stuart-brown/ArduinoShutterSpeedTester/Datasheets/2.2_TFT_LCD/lcdisplay_spi_tft_b-web.jpg

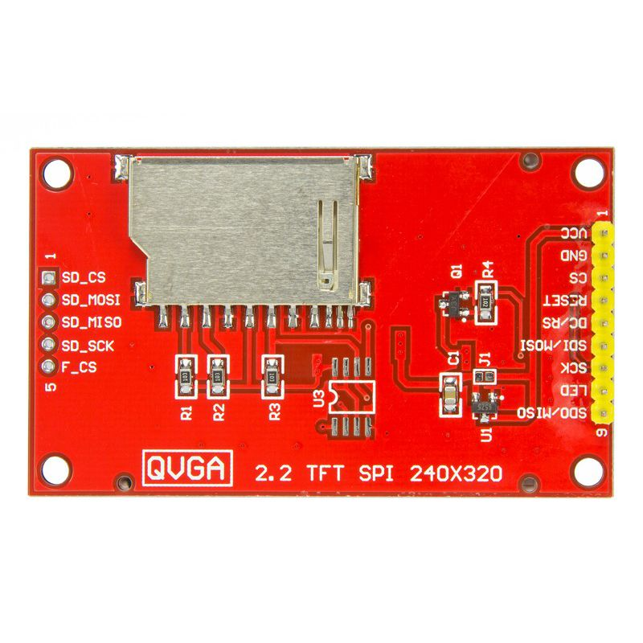
Datasheets/2.2_TFT_LCD/lcdisplay_spi_tft_b-web.jpg
