stuart-brown/ArduinoShutterSpeedTester/Datasheets/2.2_TFT_LCD/p1.jpg

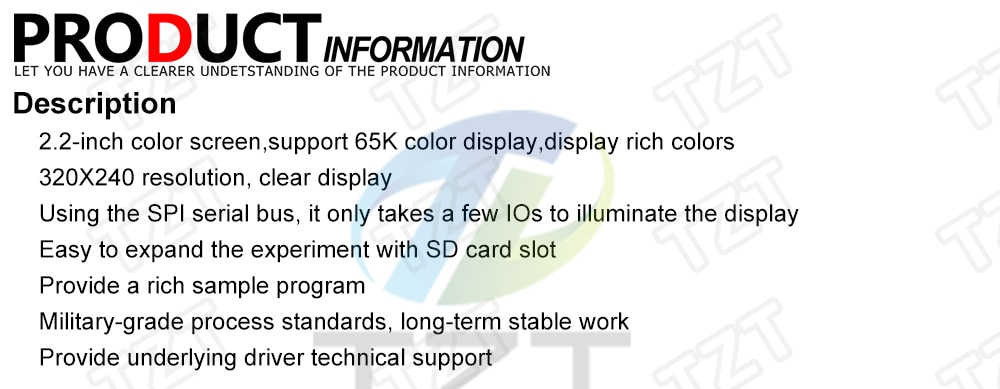
Datasheets/2.2_TFT_LCD/p1.jpg
