stuart-brown/ArduinoShutterSpeedTester/Datasheets/2.2_TFT_LCD/p3.jpg

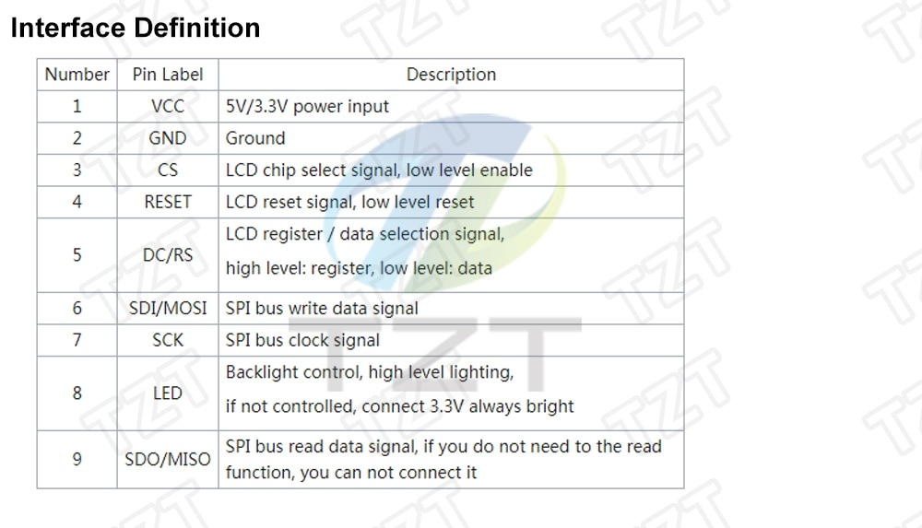
Datasheets/2.2_TFT_LCD/p3.jpg
