stuart-brown/ArduinoShutterSpeedTester/Datasheets/2.2_TFT_LCD/p4.jpg

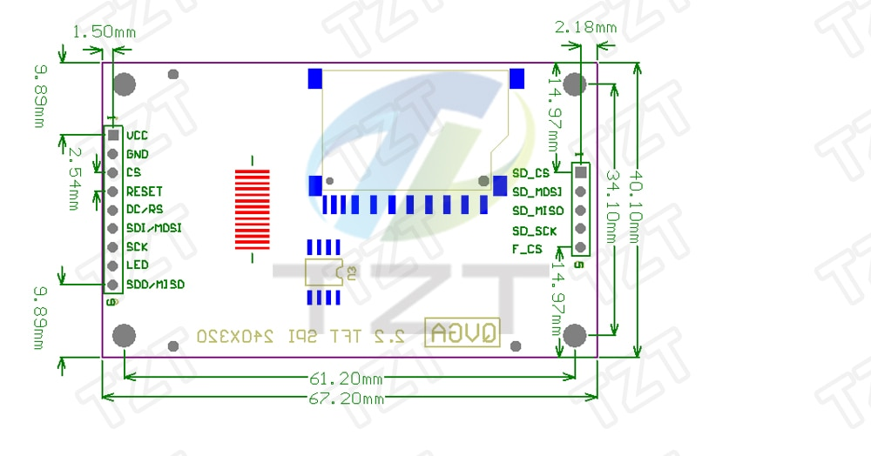
Datasheets/2.2_TFT_LCD/p4.jpg
