stuart-brown/ArduinoShutterSpeedTester/Datasheets/2.2_TFT_LCD/p8.jpg

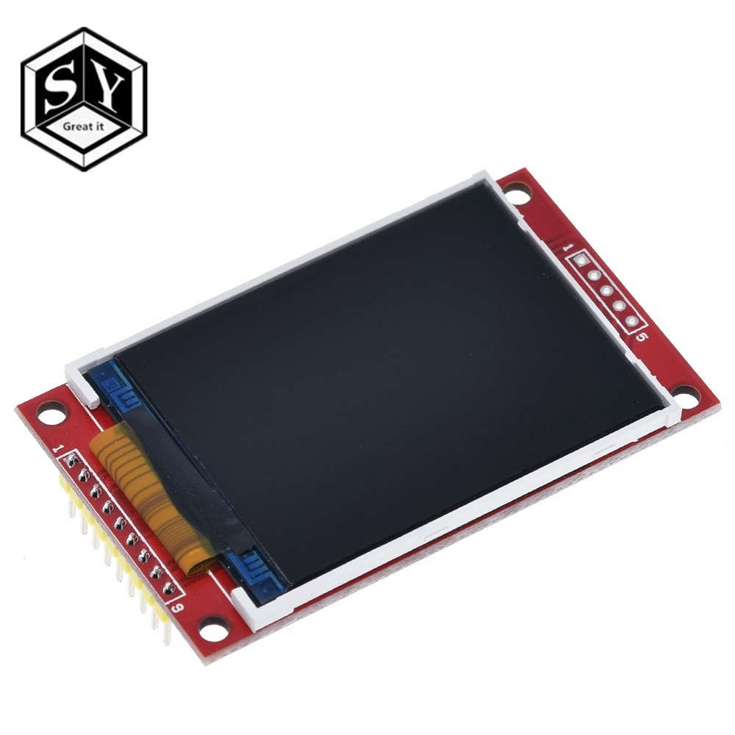
Datasheets/2.2_TFT_LCD/p8.jpg
