stuart-brown/ArduinoShutterSpeedTester/Datasheets/2.2_TFT_LCD/p10.jpg

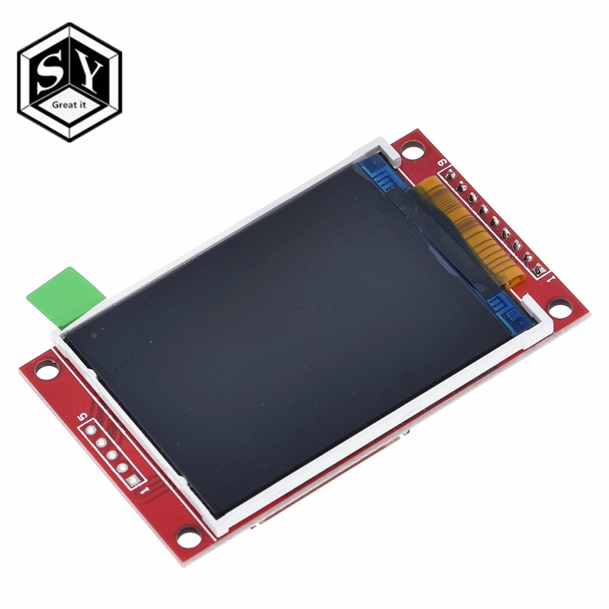
Datasheets/2.2_TFT_LCD/p10.jpg
