stuart-brown/ArduinoShutterSpeedTester/Datasheets/2.2_TFT_LCD/p11.jpg

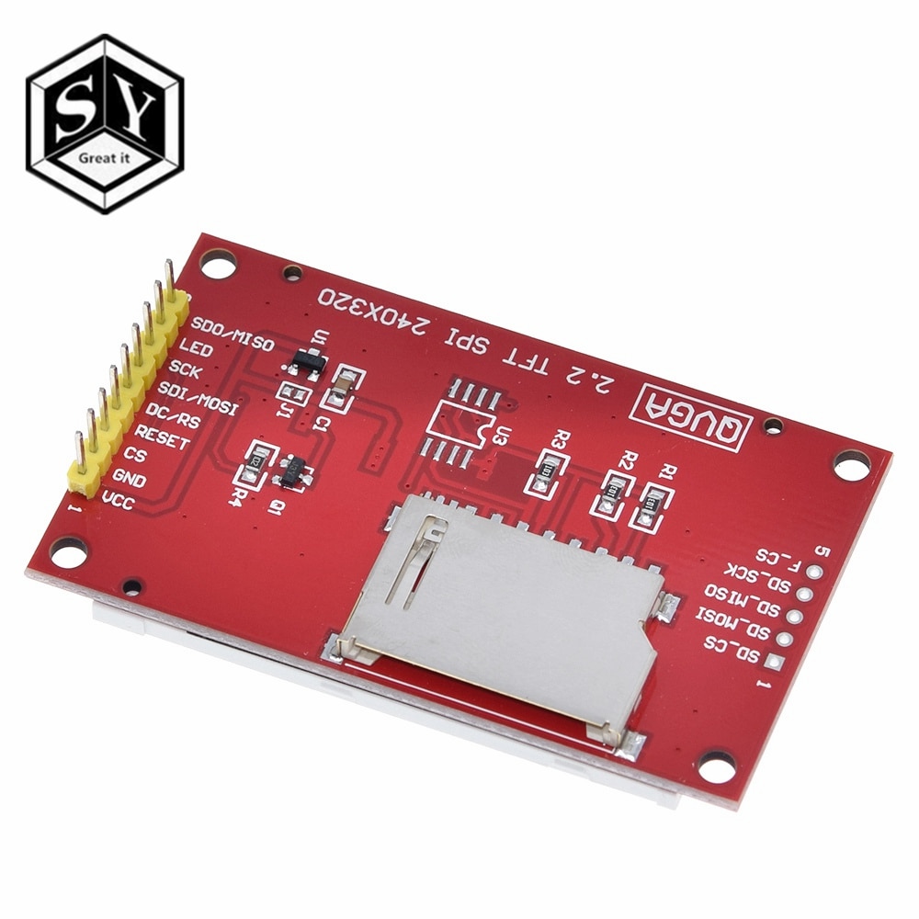
Datasheets/2.2_TFT_LCD/p11.jpg
