stuart-brown/ArduinoShutterSpeedTester/images/Version2/20230103_121651.jpg

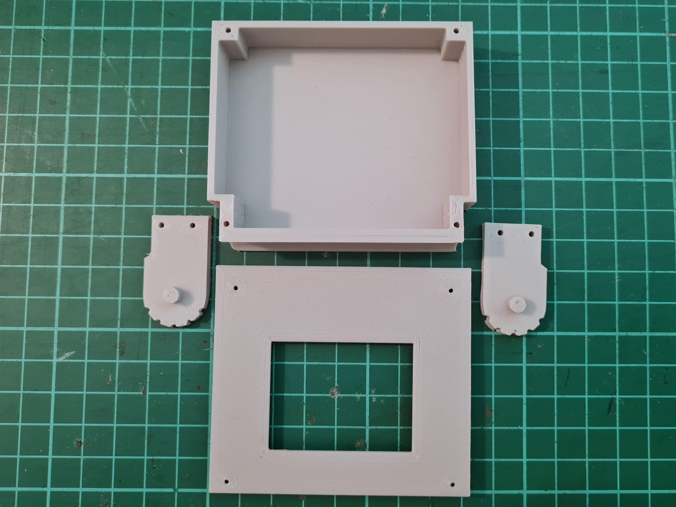
images/Version2/20230103_121651.jpg
