stuart-brown/ArduinoShutterSpeedTester/images/Version2/20230103_121801.jpg

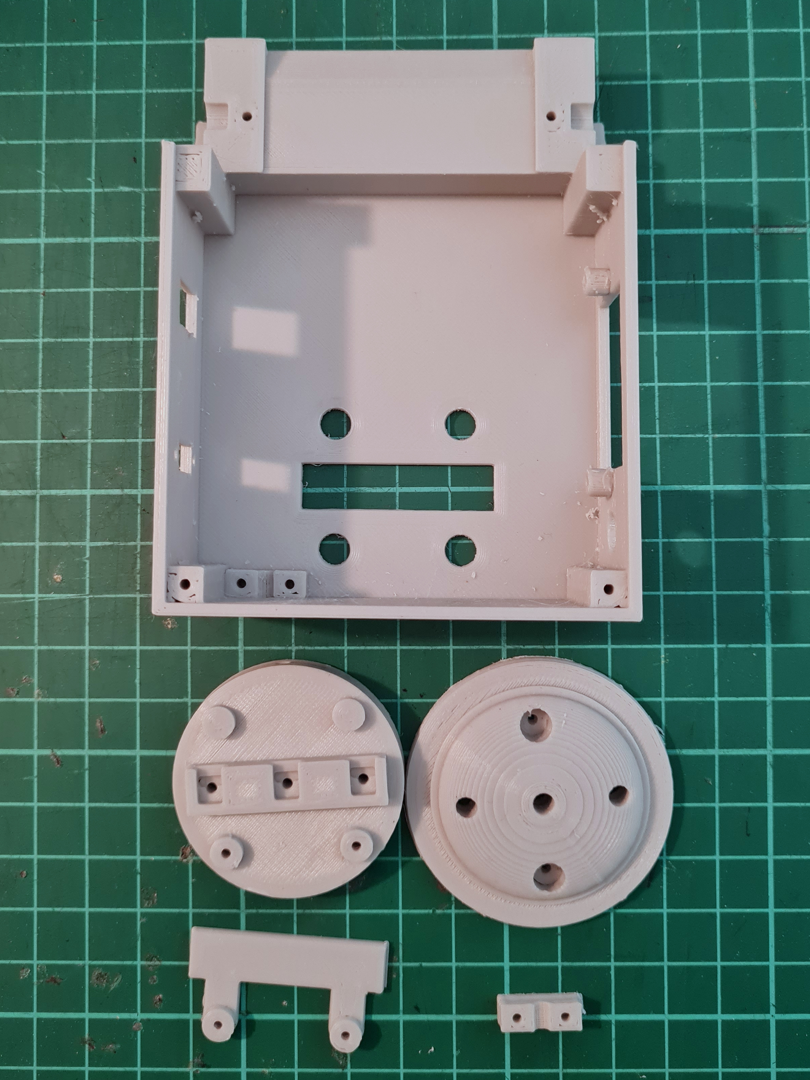
images/Version2/20230103_121801.jpg
