stuart-brown/ArduinoShutterSpeedTester/images/Version2/20230106_110242.jpg

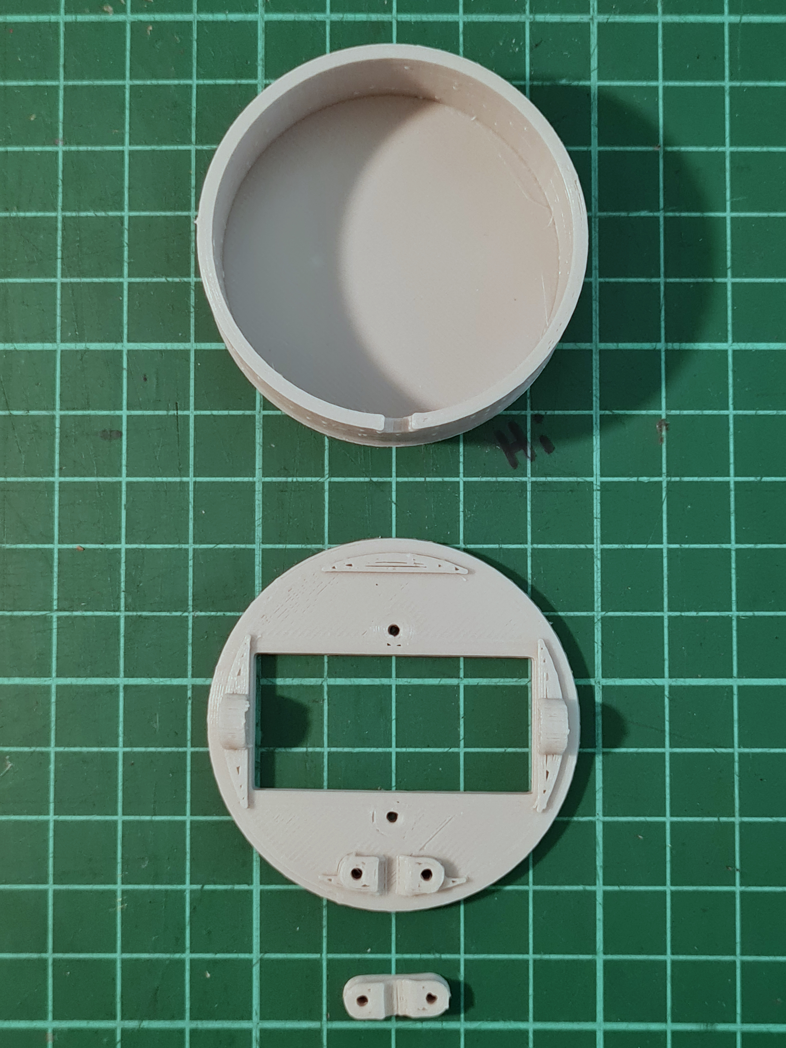
images/Version2/20230106_110242.jpg
