stuart-brown/ArduinoShutterSpeedTester/images/Version2/20230106_110354.jpg

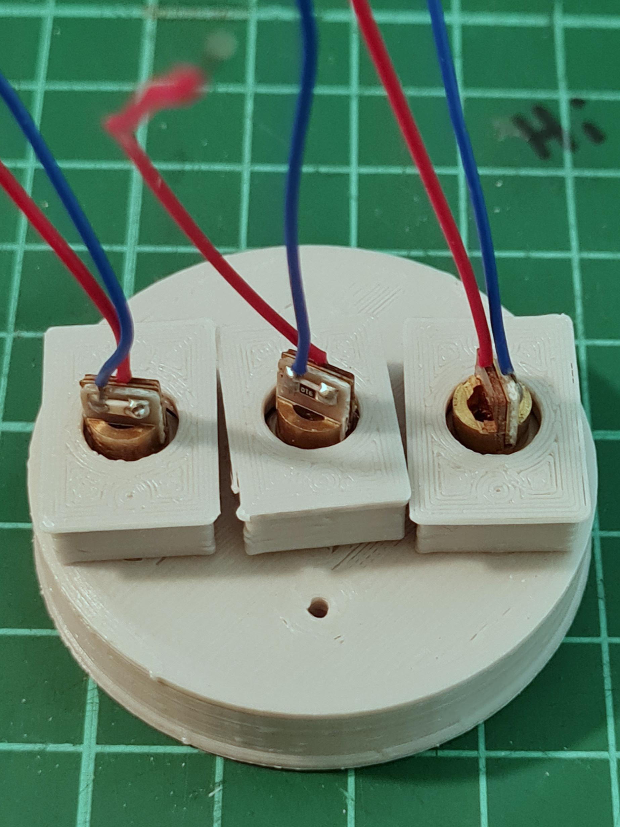
images/Version2/20230106_110354.jpg
