stuart-brown/ArduinoShutterSpeedTester/images/Version2/20230106_110403.jpg

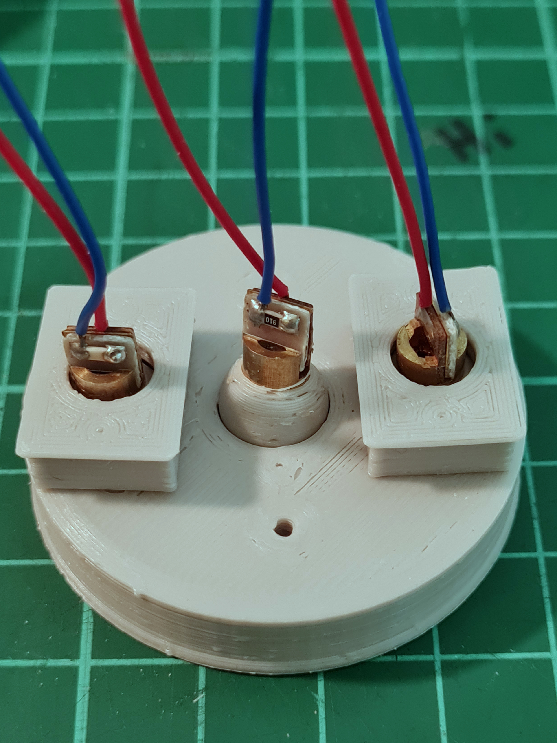
images/Version2/20230106_110403.jpg
