stuart-brown/ArduinoShutterSpeedTester/images/Version2/20230108_130916.jpg

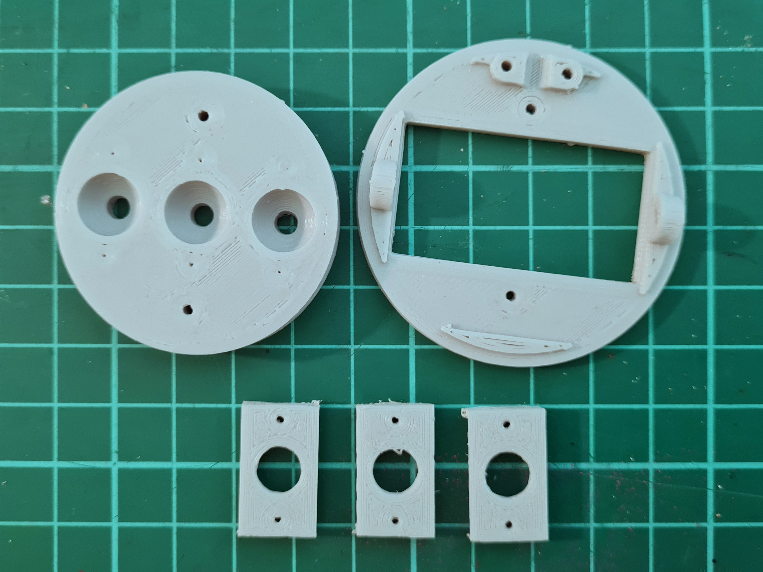
images/Version2/20230108_130916.jpg
