stuart-brown/ArduinoShutterSpeedTester/images/Version2/20230108_181926.jpg

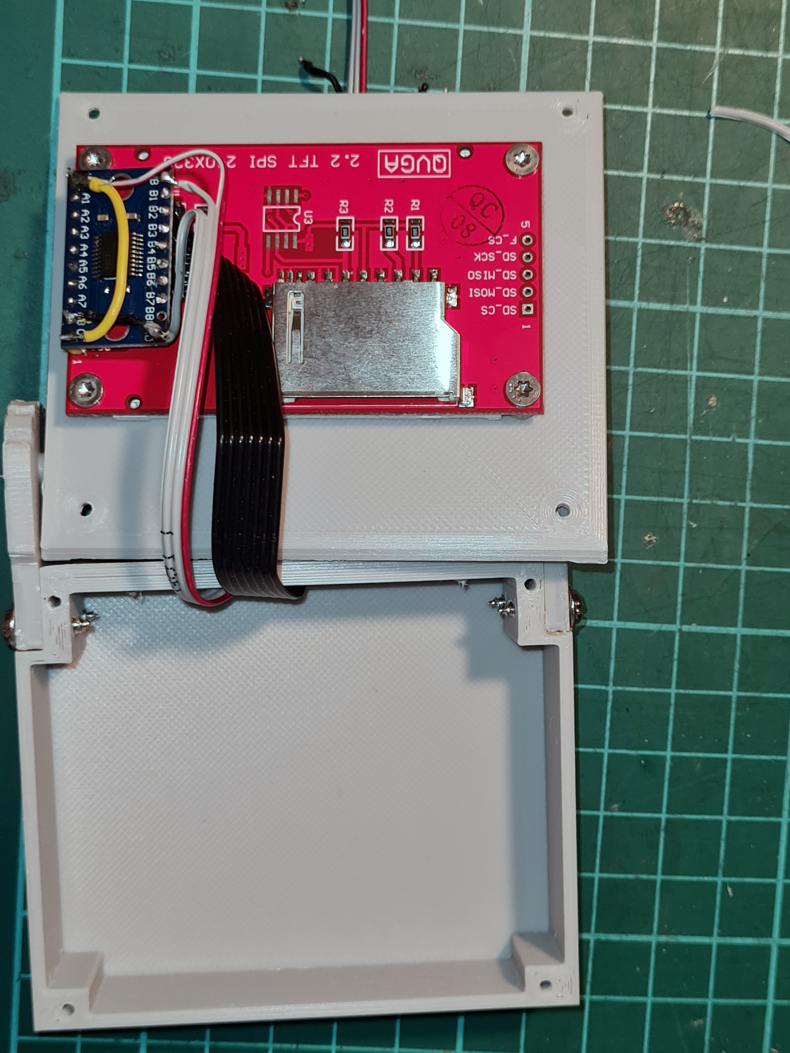
images/Version2/20230108_181926.jpg
