stuart-brown/ArduinoShutterSpeedTester/images/Version2/20230108_182143.jpg

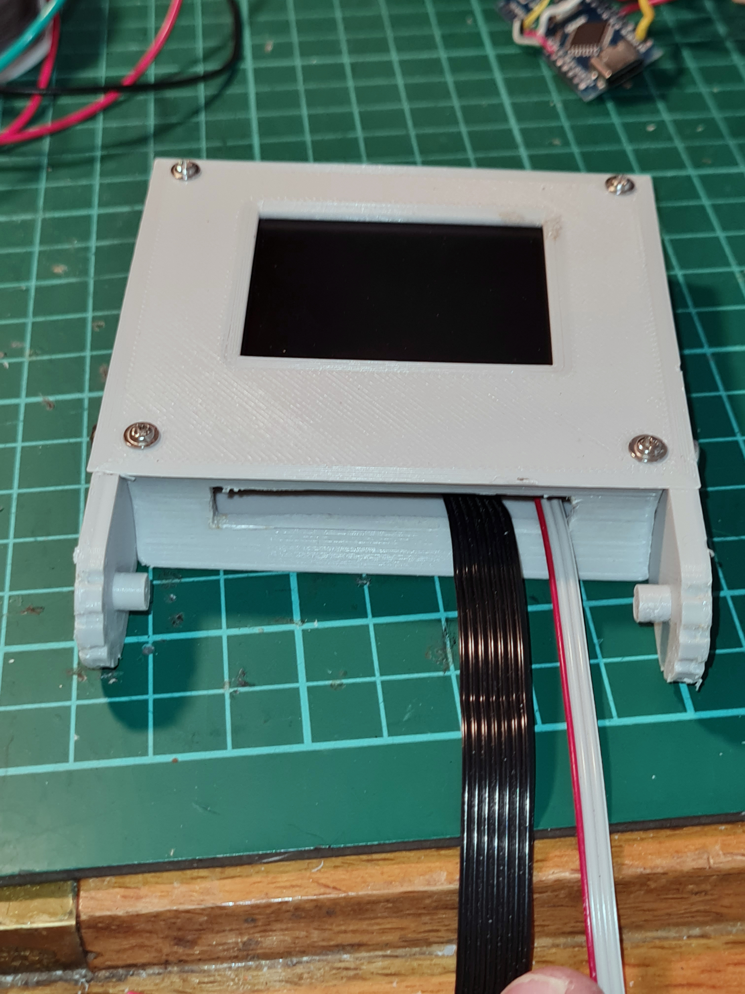
images/Version2/20230108_182143.jpg
