stuart-brown/ArduinoShutterSpeedTester/images/Version2/20230108_182205.jpg

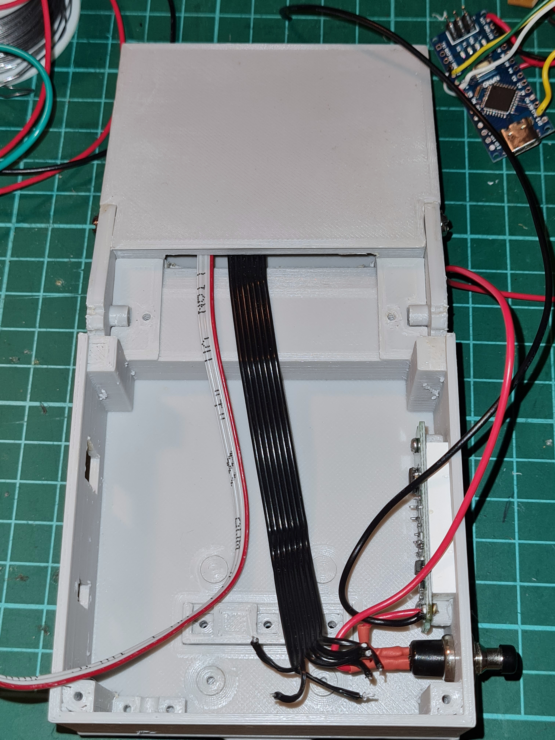
images/Version2/20230108_182205.jpg
