stuart-brown/ArduinoShutterSpeedTester/images/Version2/20230108_182213.jpg

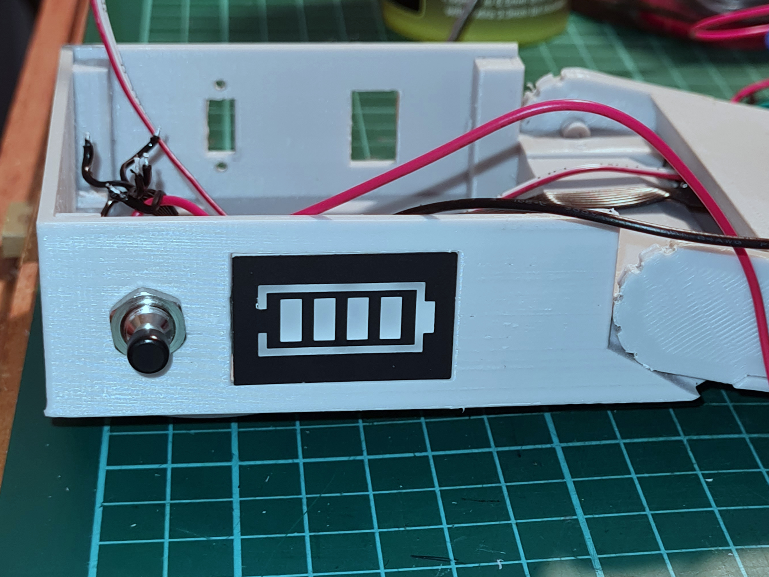
images/Version2/20230108_182213.jpg
