stuart-brown/ArduinoShutterSpeedTester/images/Version2/20230206_141832.jpg

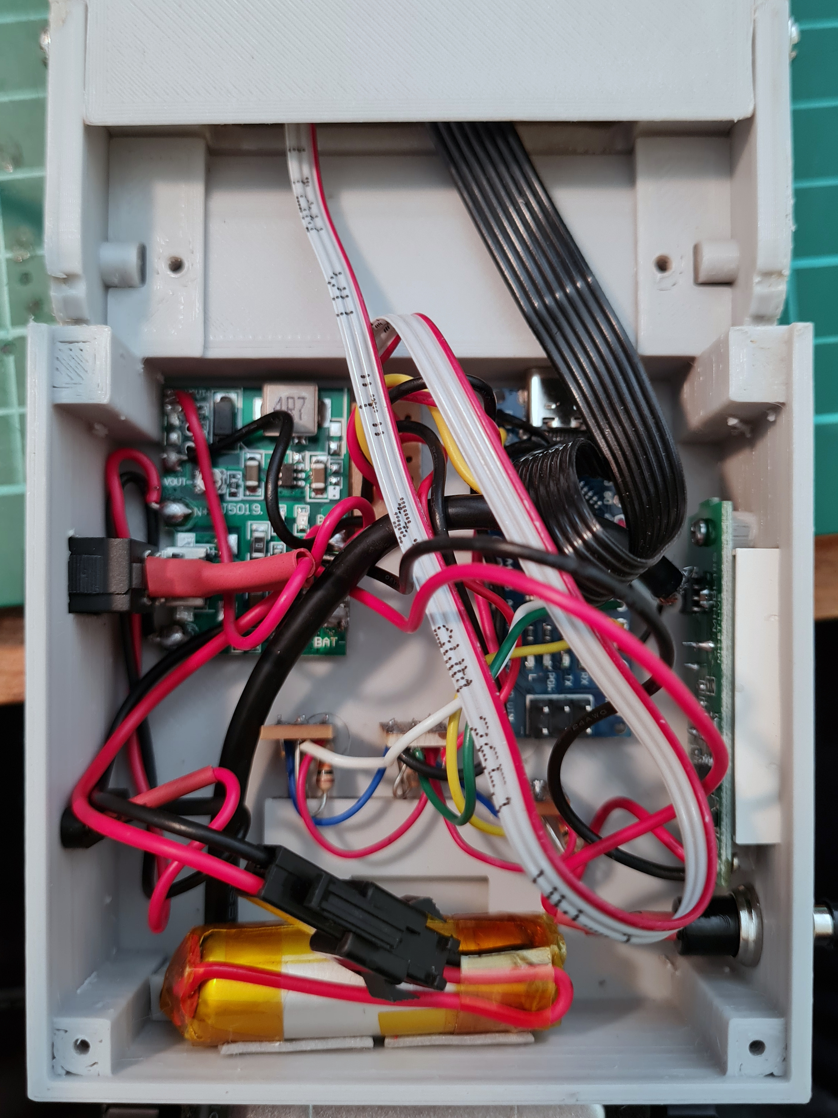
images/Version2/20230206_141832.jpg
