stuart-brown/ArduinoShutterSpeedTester/images/Version2/20230206_142243.jpg

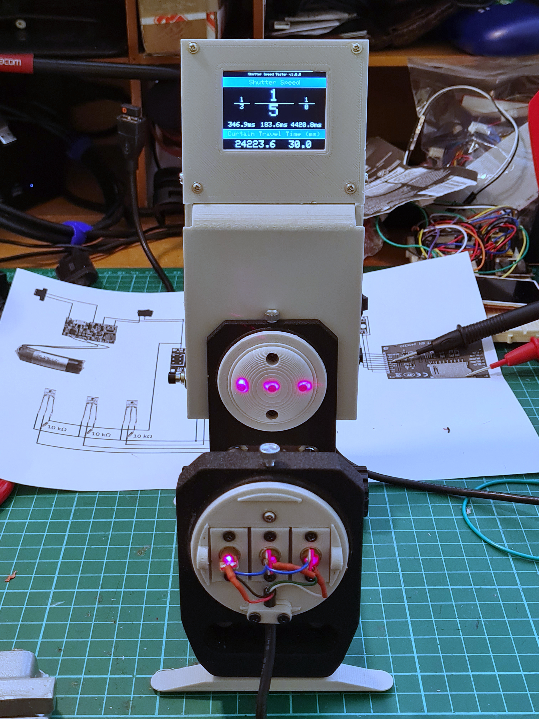
images/Version2/20230206_142243.jpg
