stuart-brown/ArduinoShutterSpeedTester/images/Version2/20230206_150605.jpg

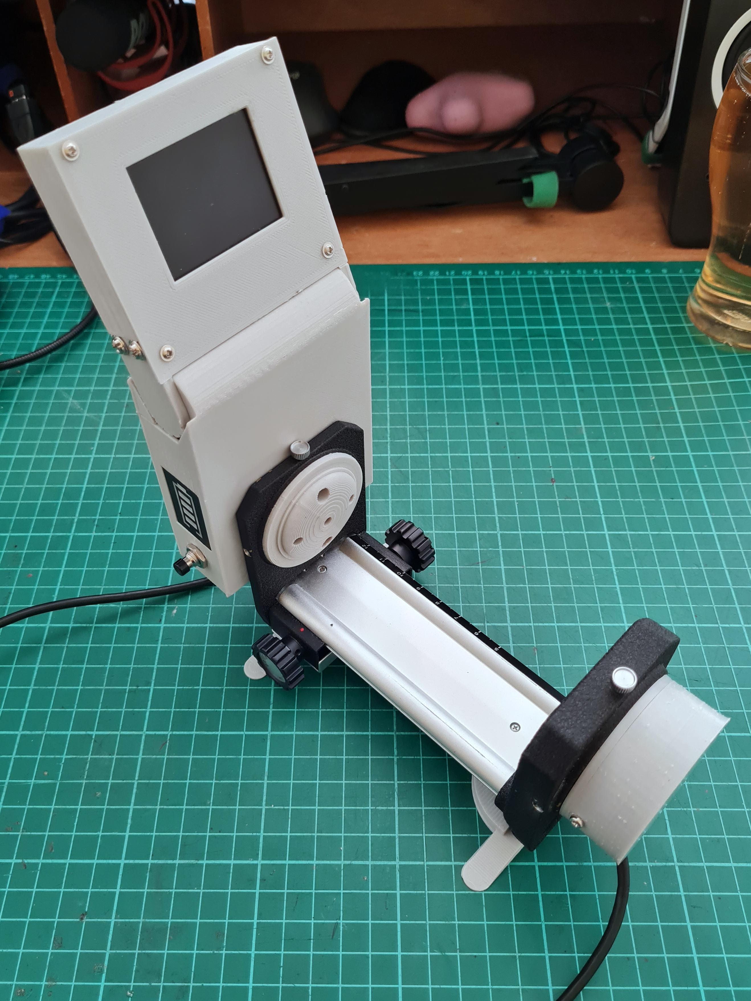
images/Version2/20230206_150605.jpg
