stuart-brown/ArduinoShutterSpeedTester/images/Version2/20230206_150620.jpg

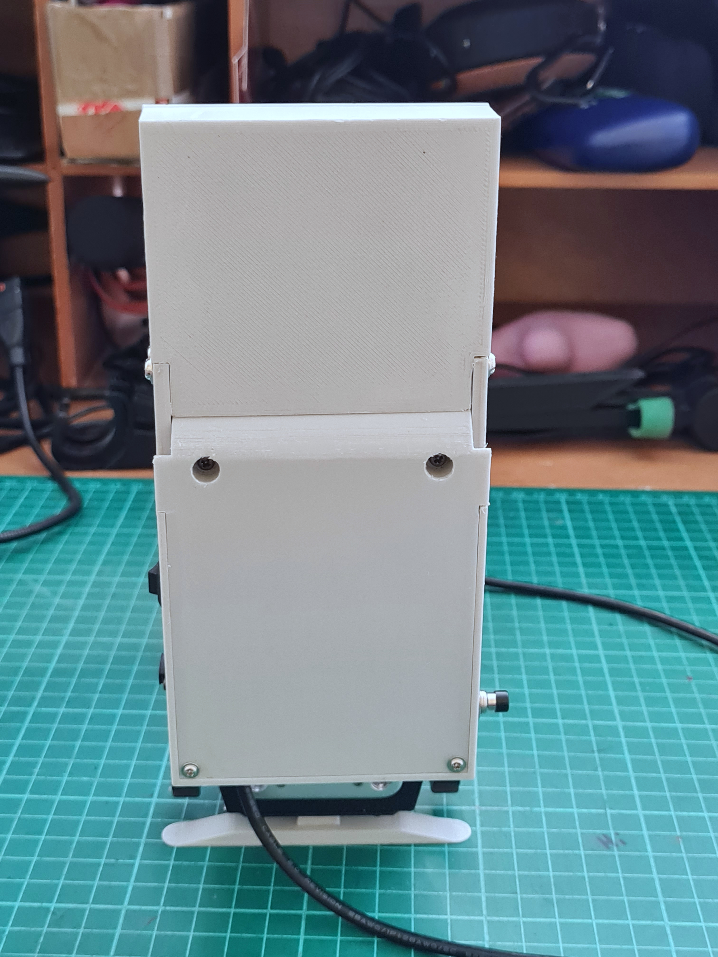
images/Version2/20230206_150620.jpg
