stuart-brown/ArduinoShutterSpeedTester/images/Version2/20230206_150632.jpg

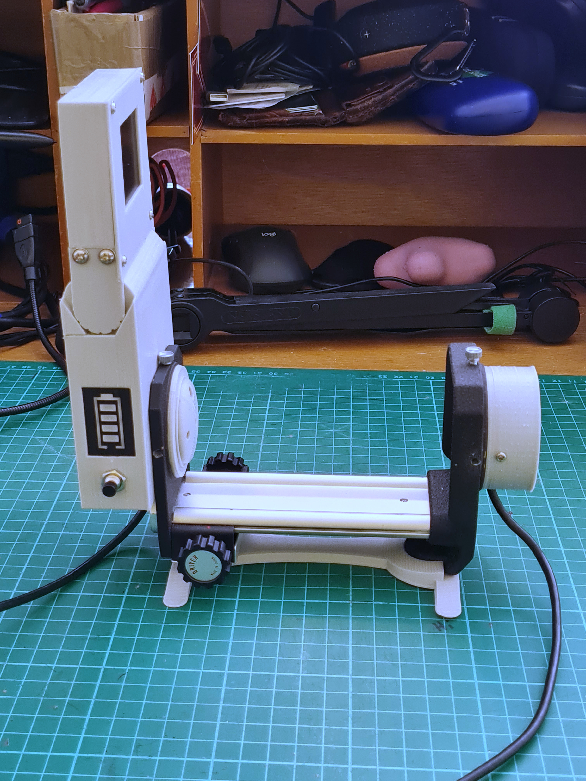
images/Version2/20230206_150632.jpg
