stuart-brown/ArduinoShutterSpeedTester/images/Version2/20230206_150637.jpg

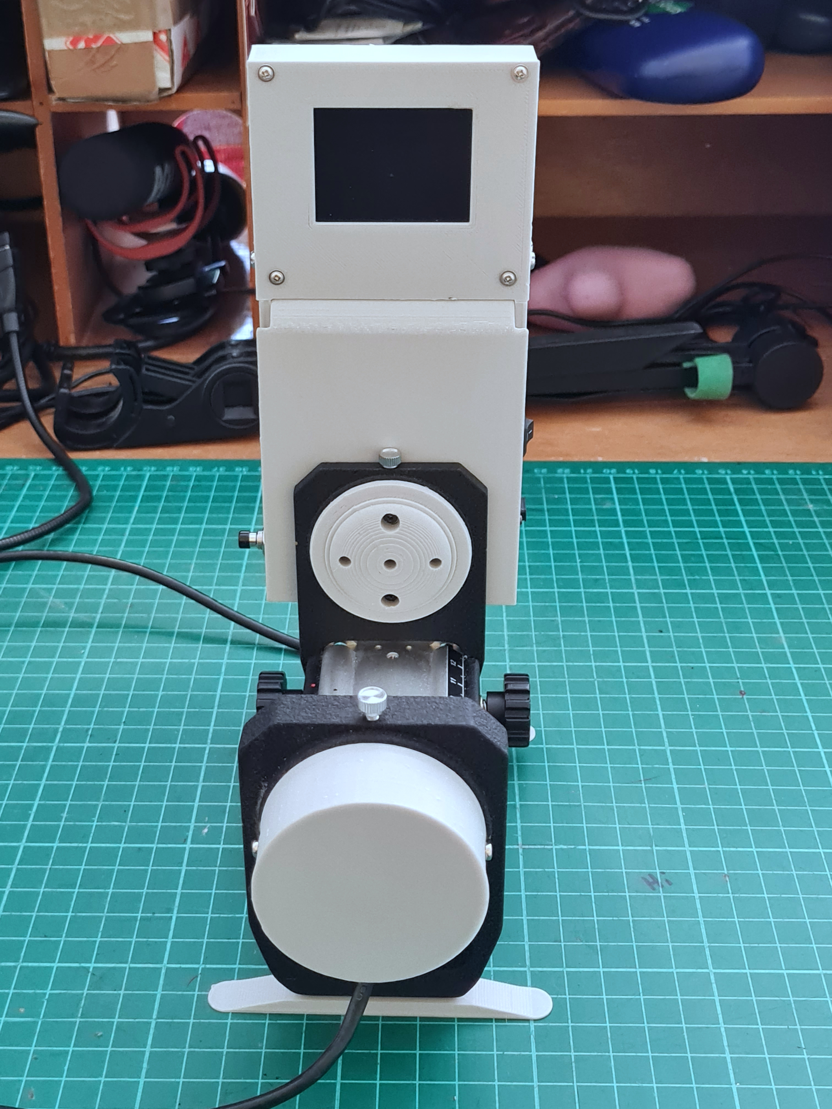
images/Version2/20230206_150637.jpg
