stuart-brown/ArduinoShutterSpeedTester/images/Version2/20230206_150643.jpg

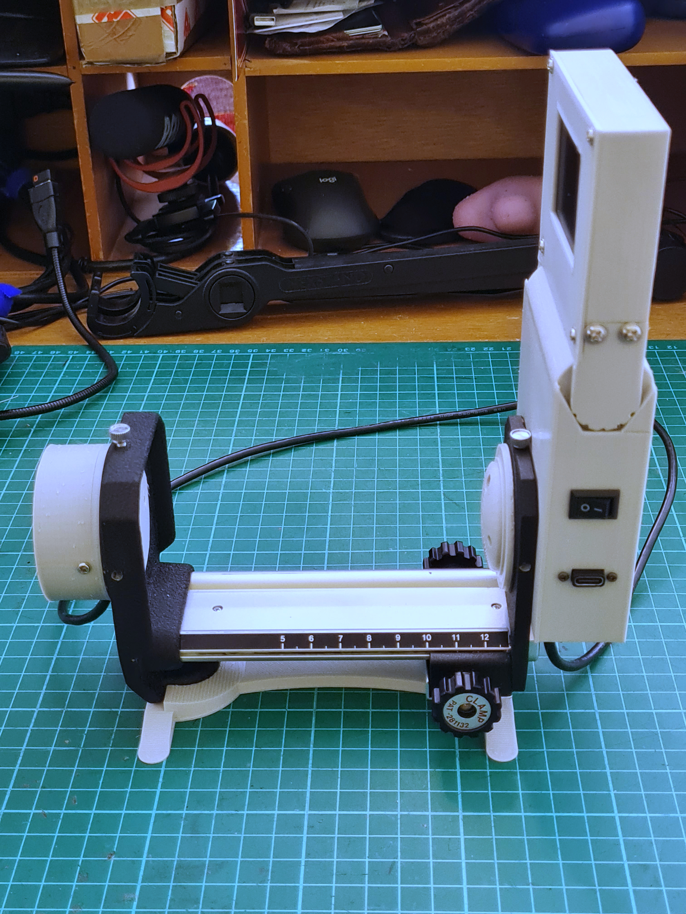
images/Version2/20230206_150643.jpg
