stuart-brown/ArduinoShutterSpeedTester/images/Version2/20230206_150703.jpg

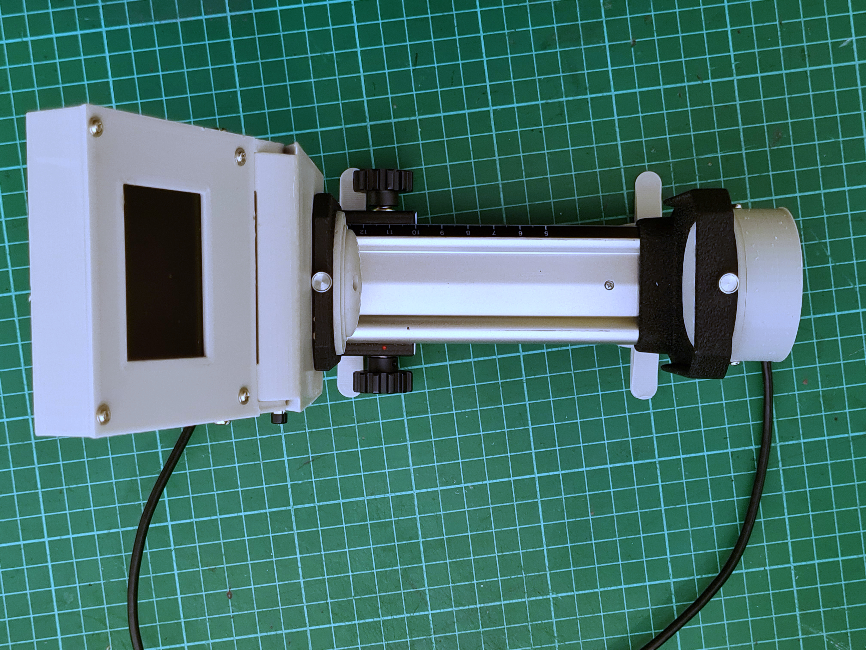
images/Version2/20230206_150703.jpg
