stuart-brown/ArduinoShutterSpeedTester/images/Version2/20230206_150759.jpg

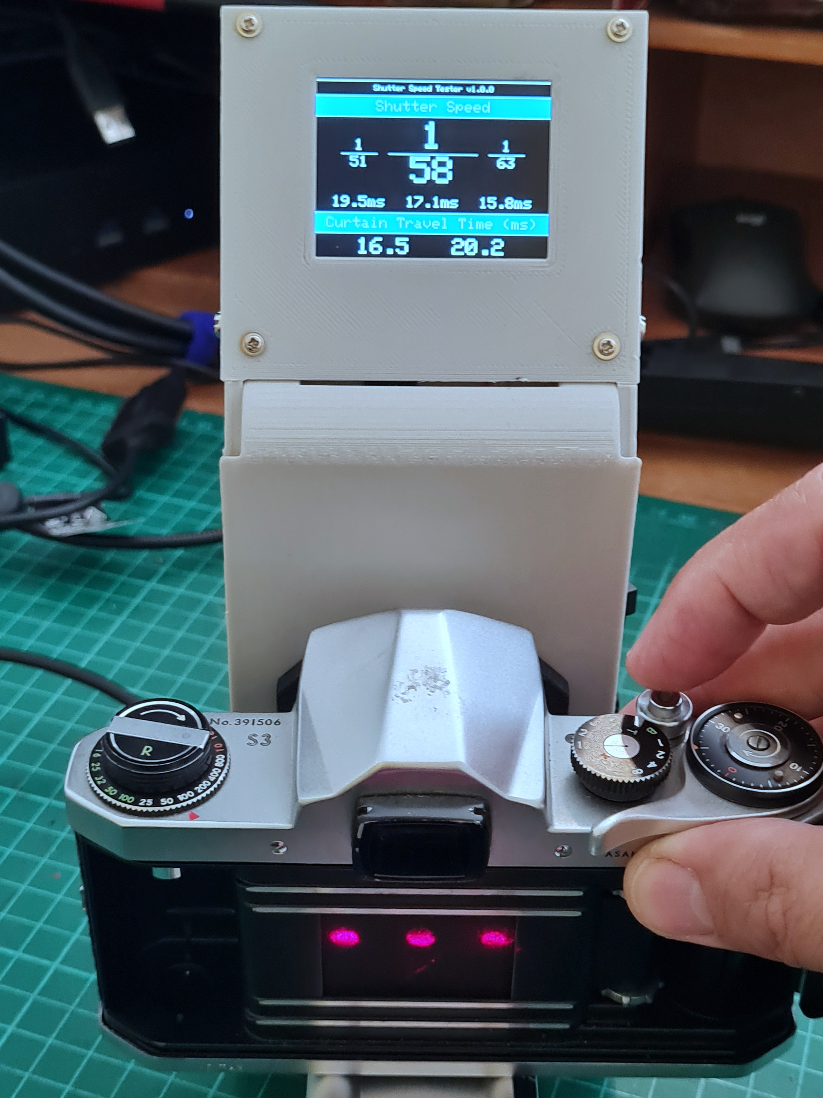
images/Version2/20230206_150759.jpg
