stuart-brown/ArduinoShutterSpeedTester/images/Version2/20230206_150818.jpg

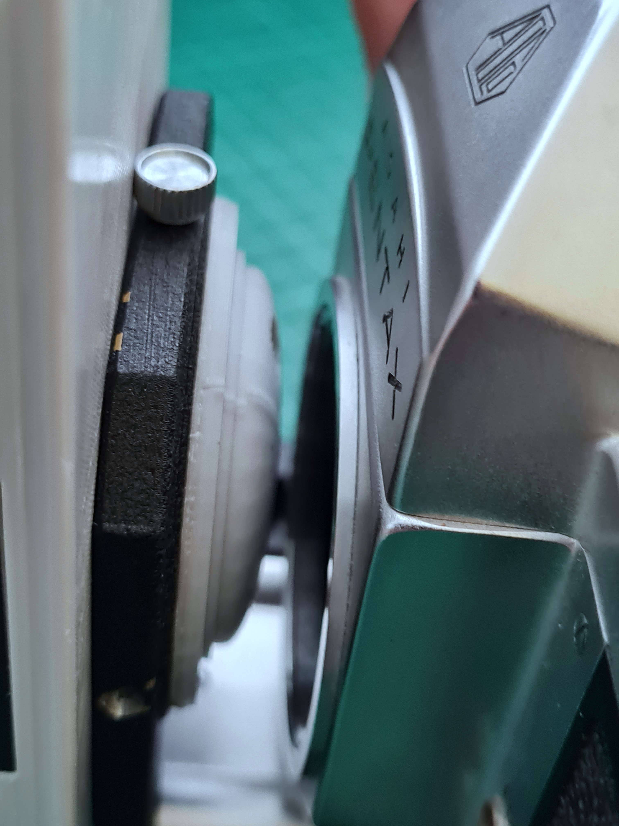
images/Version2/20230206_150818.jpg
