stuart-brown/ArduinoShutterSpeedTester/Datasheets/ISO203_Laser_Receiver/ISO203-Laser-Receiver-Operation.png

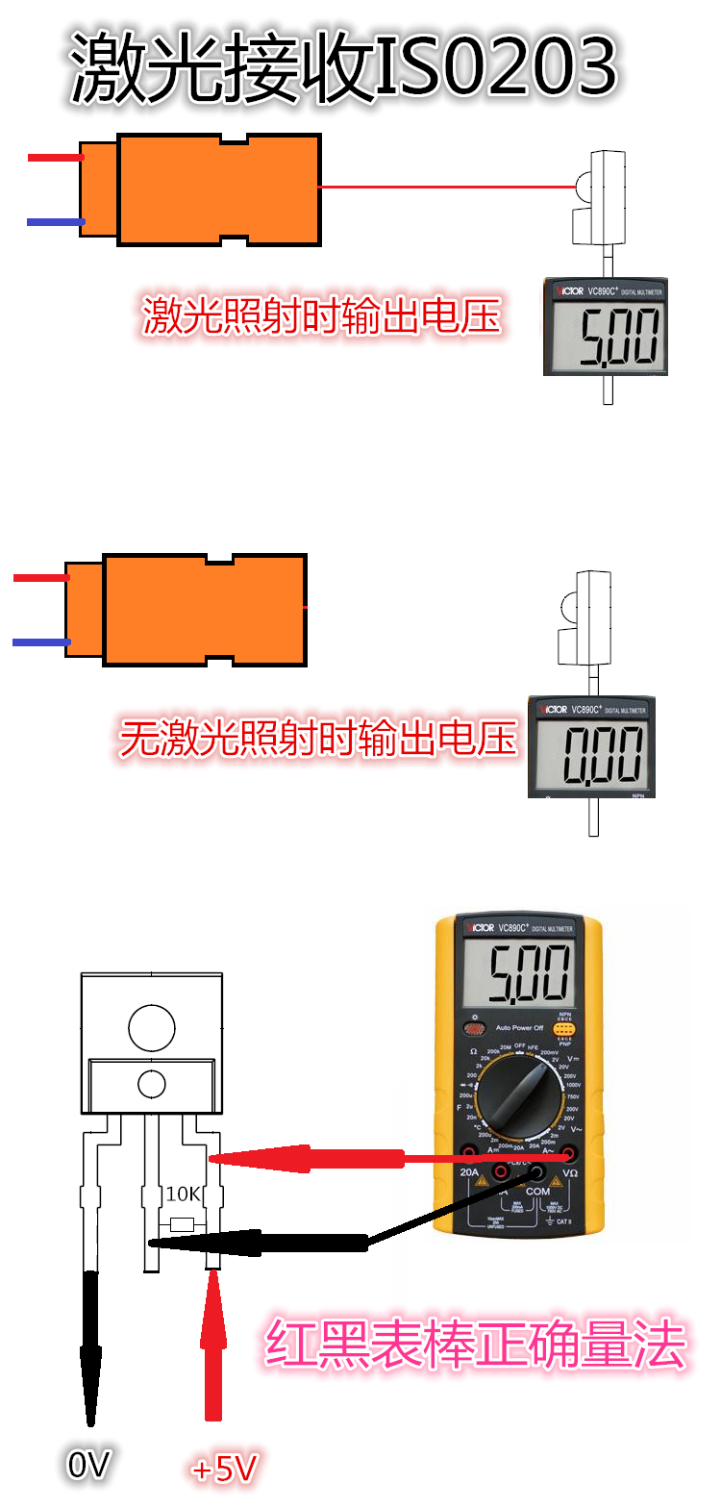
Datasheets/ISO203_Laser_Receiver/ISO203-Laser-Receiver-Operation.png
