stuart-brown/ArduinoShutterSpeedTester/WiringDiagram/10k.jpg

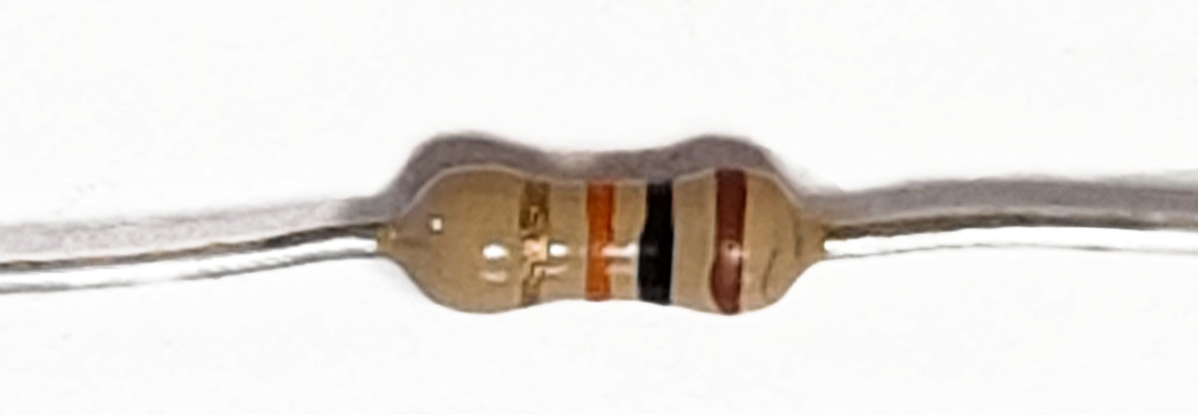
WiringDiagram/10k.jpg
