stuart-brown/ArduinoShutterSpeedTester/WiringDiagram/47Ohm.jpg

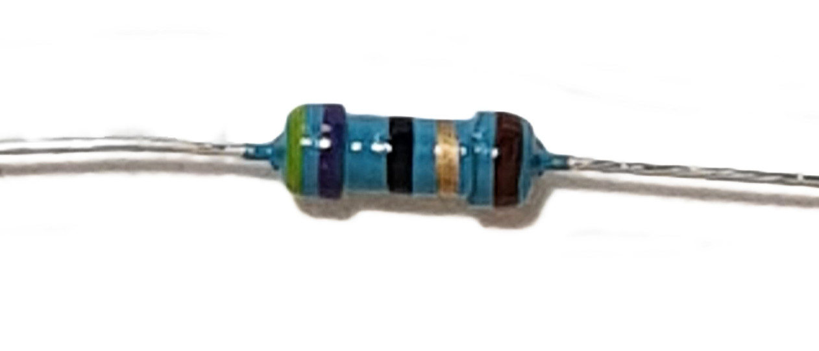
WiringDiagram/47Ohm.jpg
