stuart-brown/ArduinoShutterSpeedTester/WiringDiagram/ChargerModule.jpg

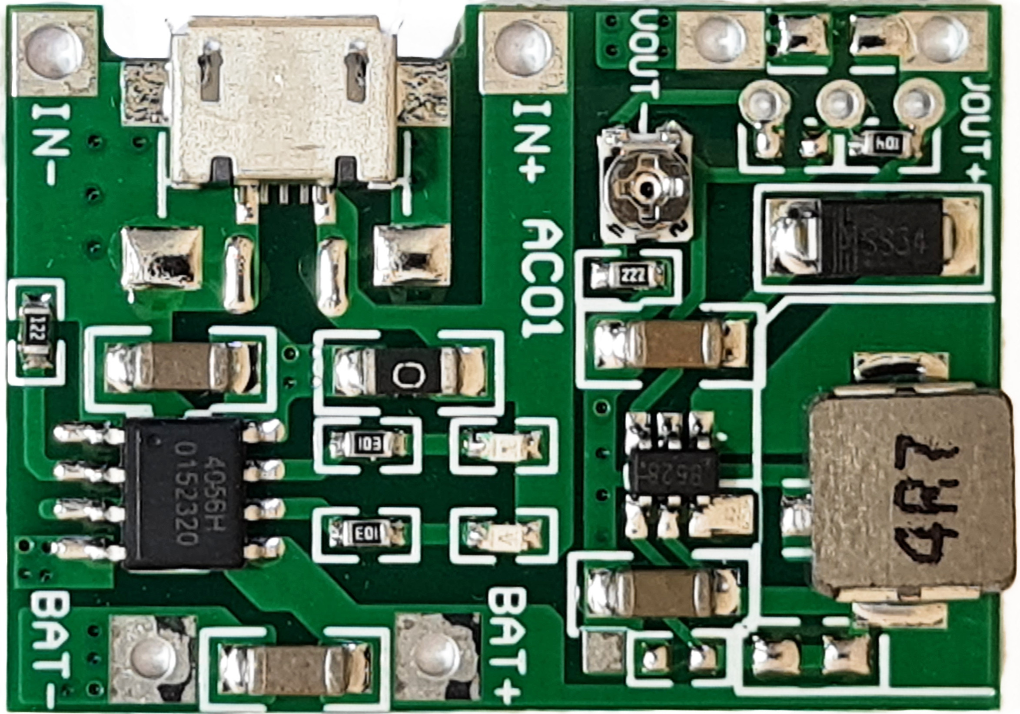
WiringDiagram/ChargerModule.jpg
