stuart-brown/ArduinoShutterSpeedTester/WiringDiagram/Display.jpg

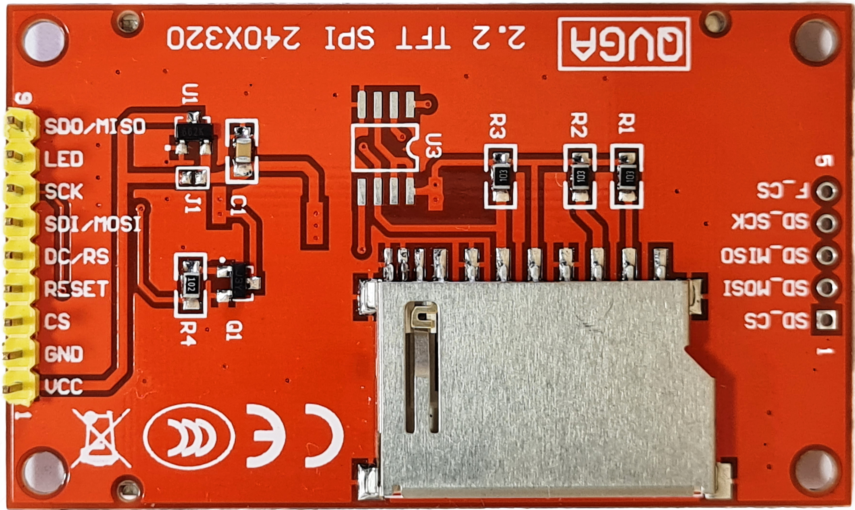
WiringDiagram/Display.jpg
