stuart-brown/ArduinoShutterSpeedTester/WiringDiagram/LaserSensor.jpg

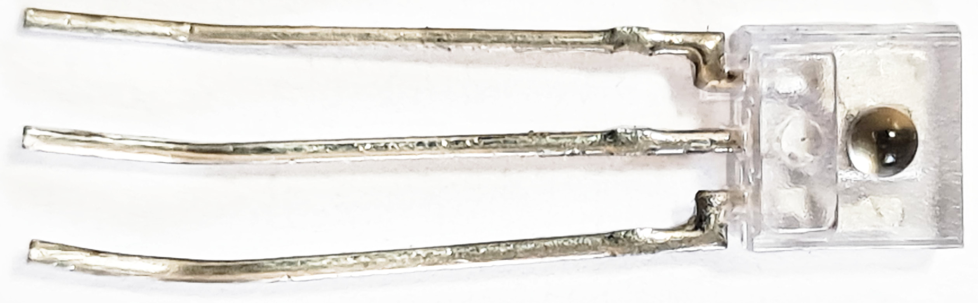
WiringDiagram/LaserSensor.jpg
