stuart-brown/ArduinoShutterSpeedTester/WiringDiagram/LevelShifter.jpg

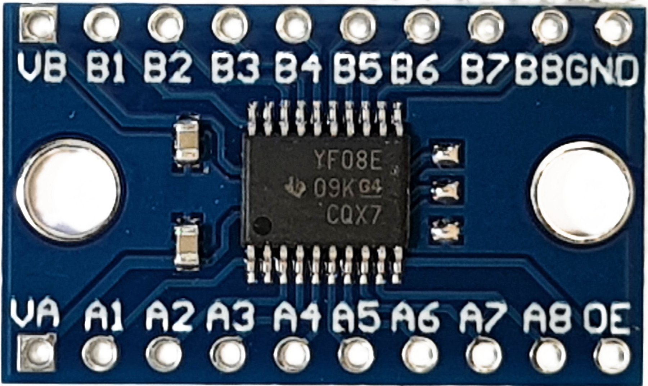
WiringDiagram/LevelShifter.jpg
