stuart-brown/ArduinoShutterSpeedTester/WiringDiagram/Switch.jpg

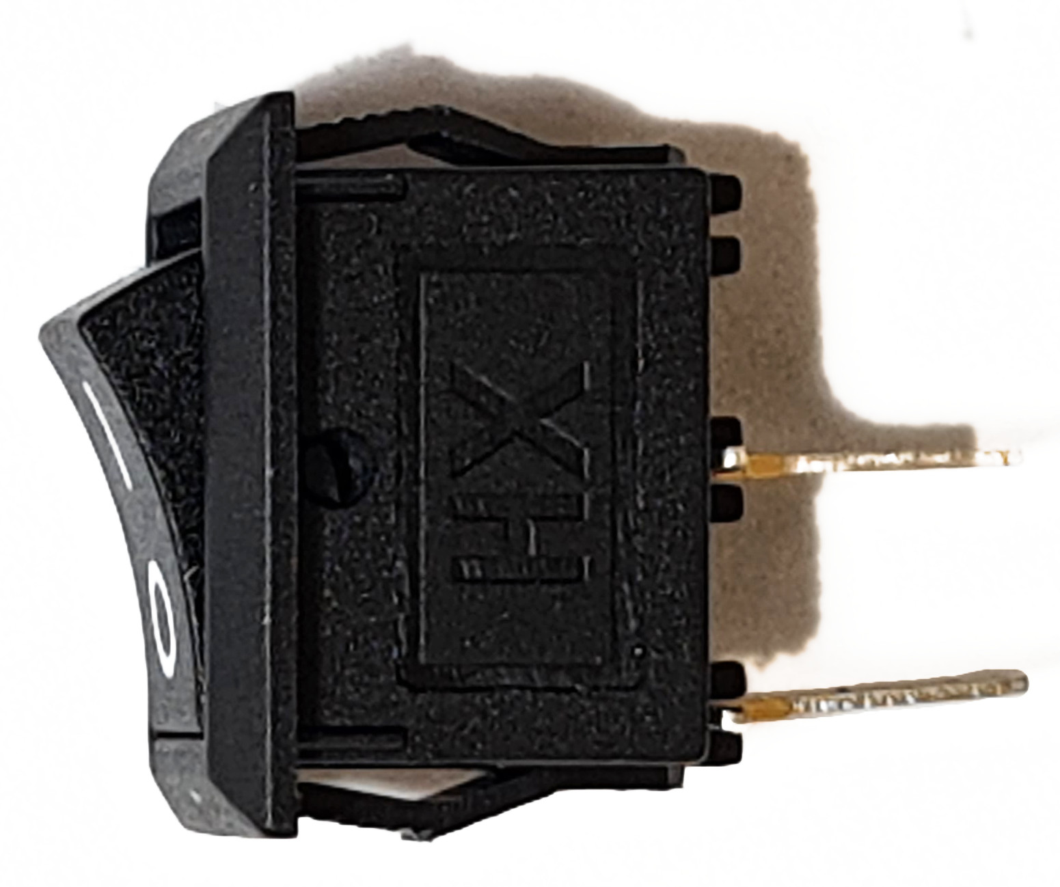
WiringDiagram/Switch.jpg
